nchourrout/rokuremote/2.png

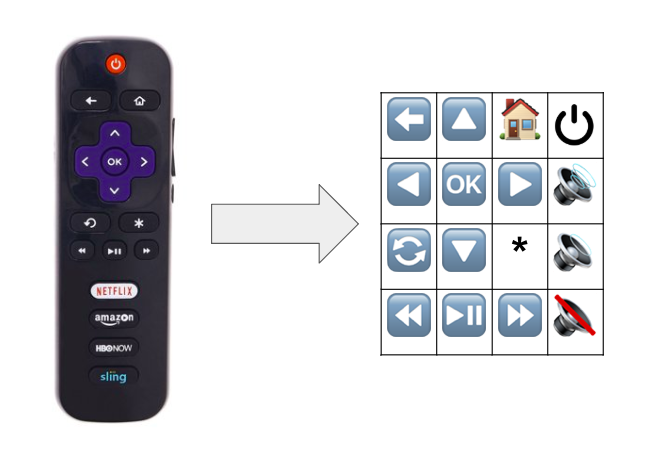
2.png
